pablovazquezmartinez/Digital-Photo-Frame-ESP32/photos/photo1.jpeg

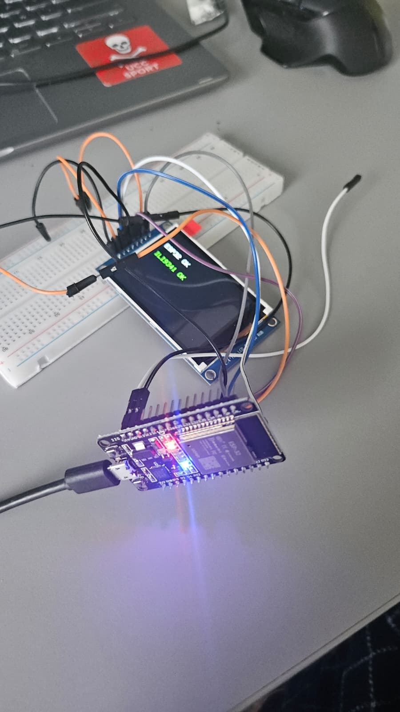
photos/photo1.jpeg
