pablovazquezmartinez/Digital-Photo-Frame-ESP32/photos/photo2.jpeg

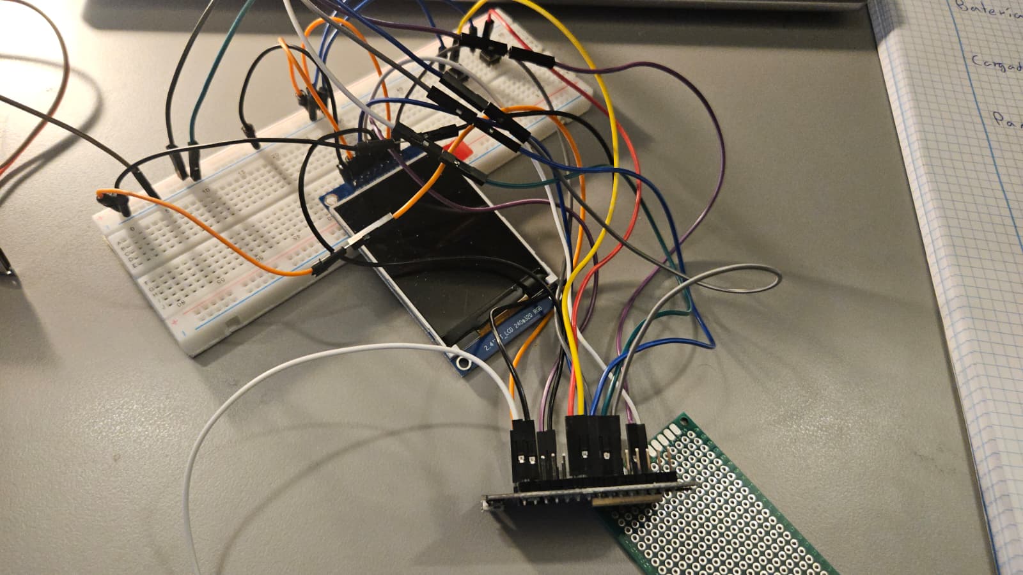
photos/photo2.jpeg
