pablovazquezmartinez/Digital-Photo-Frame-ESP32/photos/photo3.jpeg

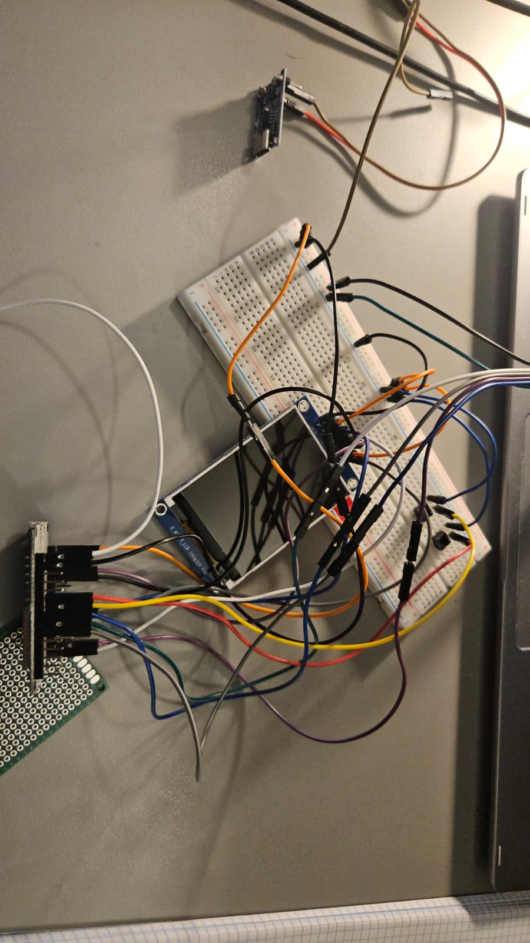
photos/photo3.jpeg
