pablovazquezmartinez/Digital-Photo-Frame-ESP32/photos/photo4.jpeg

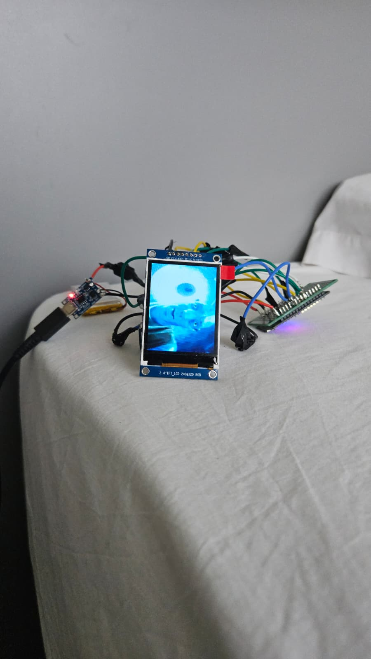
photos/photo4.jpeg
